MacNite/HiveInside/firmware-nrf54lm20a/src/mic.c

/* mic.c — see mic.h.
 *
 * The nRF54's PDM peripheral filters PDM to 16-bit PCM in hardware, so this
 * module only gathers PCM blocks through Zephyr's dmic API and runs the same
 * dBFS + FFT band analysis as HiveScale, so a band value means the same thing
 * across the ecosystem.
 *
 * The PDM clock only runs between DMIC_TRIGGER_START and _STOP, so the
 * microphone (powered from nPM1300 LDO1 — see power.c) draws its idle current
 * outside the ~0.7 s capture.
 *
 * The PDM controller is resolved by compatible, not by node label: any enabled
 * `nordic,nrf-pdm` node is used (the Sense board wires it to the on-board
 * MSM261DGT006). If the devicetree has none enabled, the module compiles to a
 * stub and the readout reports the mic absent.
 */
#include "mic.h"

#include "fft.h"
#include "hive_config.h"

#include <errno.h>
#include <math.h>
#include <zephyr/audio/dmic.h>
#include <zephyr/devicetree.h>
#include <zephyr/kernel.h>
#include <zephyr/sys/printk.h>

#if ENABLE_MIC && DT_HAS_COMPAT_STATUS_OKAY(nordic_nrf_pdm)

#define MIC_NODE DT_COMPAT_GET_ANY_STATUS_OKAY(nordic_nrf_pdm)

#define BLOCK_BYTES     (MIC_BLOCK_SAMPLES * sizeof(int16_t))
#define BLOCK_COUNT     6
#define READ_TIMEOUT_MS 1000

#define FULL_SCALE   32768.0f /* 16-bit PCM */
#define SILENCE_DBFS (-200.0f)

static const struct device *const dmic_dev = DEVICE_DT_GET(MIC_NODE);

K_MEM_SLAB_DEFINE_STATIC(mic_slab, BLOCK_BYTES, BLOCK_COUNT, 4);

/* FFT scratch + PCM staging, static like the accel path. */
static float fft_re[MIC_FFT_SAMPLE_COUNT];
static float fft_im[MIC_FFT_SAMPLE_COUNT];
static int16_t fft_pcm[MIC_FFT_SAMPLE_COUNT];

int mic_stream_start(void)
{
	if (!device_is_ready(dmic_dev)) {
		return -ENODEV;
	}
	struct pcm_stream_cfg stream = {
		.pcm_rate = MIC_SAMPLE_RATE, .pcm_width = 16,
		.block_size = BLOCK_BYTES, .mem_slab = &mic_slab,
	};
	struct dmic_cfg cfg = {
		.io = { .min_pdm_clk_freq = 1000000, .max_pdm_clk_freq = 3500000,
			.min_pdm_clk_dc = 40, .max_pdm_clk_dc = 60 },
		.streams = &stream,
		.channel = { .req_num_streams = 1, .req_num_chan = 1 },
	};
	cfg.channel.req_chan_map_lo = dmic_build_channel_map(0, 0, PDM_CHAN_LEFT);
	int err = dmic_configure(dmic_dev, &cfg);
	return err != 0 ? err : dmic_trigger(dmic_dev, DMIC_TRIGGER_START);
}

int mic_stream_read(void **buf, uint32_t *size, int32_t timeout_ms)
{
	return dmic_read(dmic_dev, 0, buf, size, timeout_ms);
}

void mic_stream_release(void *buf)
{
	k_mem_slab_free(&mic_slab, buf);
}

void mic_stream_stop(void)
{
	(void)dmic_trigger(dmic_dev, DMIC_TRIGGER_STOP);
}

static float band_energy_dbfs(const float *mag, float lo_hz, float hi_hz,
			      float norm)
{
	/* Parseval sum (no /count) so the value reflects real in-band acoustic
	 * energy and is comparable between bands of different widths — same
	 * convention as HiveScale. */
	float amp = hive_fft_band_amplitude(mag, MIC_FFT_SAMPLE_COUNT,
					    (float)MIC_SAMPLE_RATE, lo_hz,
					    hi_hz, norm, false);
	return amp > 0.0f ? 20.0f * log10f(amp) : SILENCE_DBFS;
}

static void compute_bands(size_t count, struct measurement *m)
{
	size_t n = MIN(count, (size_t)MIC_FFT_SAMPLE_COUNT);

	/* Centre the block on its mean so microphone DC bias does not leak
	 * through the Hann window side-lobes into the low bands. */
	float mean = 0.0f;

	for (size_t i = 0; i < n; i++) {
		mean += (float)fft_pcm[i];
	}
	if (n > 0) {
		mean /= (float)n;
	}
	for (size_t i = 0; i < n; i++) {
		fft_re[i] = ((float)fft_pcm[i] - mean) / FULL_SCALE;
		fft_im[i] = 0.0f;
	}
	for (size_t i = n; i < MIC_FFT_SAMPLE_COUNT; i++) {
		fft_re[i] = 0.0f;
		fft_im[i] = 0.0f;
	}

	hive_fft_hann(fft_re, MIC_FFT_SAMPLE_COUNT);
	hive_fft_magnitude(fft_re, fft_im, MIC_FFT_SAMPLE_COUNT);

	const float norm = ((float)MIC_FFT_SAMPLE_COUNT / 2.0f) * 0.5f;

	m->mic_band_sub_bass_dbfs = band_energy_dbfs(fft_re, MIC_BAND_SUBBASS_LO, MIC_BAND_SUBBASS_HI, norm);
	m->mic_band_hum_dbfs      = band_energy_dbfs(fft_re, MIC_BAND_HUM_LO, MIC_BAND_HUM_HI, norm);
	m->mic_band_piping_dbfs   = band_energy_dbfs(fft_re, MIC_BAND_PIPING_LO, MIC_BAND_PIPING_HI, norm);
	m->mic_band_stress_dbfs   = band_energy_dbfs(fft_re, MIC_BAND_STRESS_LO, MIC_BAND_STRESS_HI, norm);
	m->mic_band_high_dbfs     = band_energy_dbfs(fft_re, MIC_BAND_HIGH_LO, MIC_BAND_HIGH_HI, norm);
}

void mic_read(struct measurement *m)
{
	m->mic_ok = false;

	/* link's session gate is held for the complete measurement cycle, keeping
	 * this one-shot capture exclusive with audio's use of the PDM controller. */
	int err = mic_stream_start();
	if (err != 0) {
		printk("[MIC] start failed (%d)\n", err);
		return;
	}

	float sum = 0.0f, sum_sq = 0.0f;
	int16_t mn = INT16_MAX, mx = INT16_MIN;
	uint32_t count = 0;
	size_t fft_count = 0;
	unsigned block = 0;

	while (count < MIC_SAMPLE_FRAMES) {
		void *buf;
		uint32_t size;

		err = mic_stream_read(&buf, &size, READ_TIMEOUT_MS);
		if (err != 0) {
			printk("[MIC] read failed (%d) after %u frames\n", err,
			       (unsigned)count);
			break;
		}

		if (block++ < MIC_WARMUP_BLOCKS) {
			/* Discard: PDM filter + mic output still settling. */
			mic_stream_release(buf);
			continue;
		}

		const int16_t *pcm = buf;
		size_t frames = size / sizeof(int16_t);

		for (size_t i = 0; i < frames && count < MIC_SAMPLE_FRAMES; i++) {
			int16_t s = pcm[i];
			float f = (float)s;

			sum += f;
			sum_sq += f * f;
			if (s > mx) {
				mx = s;
			}
			if (s < mn) {
				mn = s;
			}
			if (fft_count < MIC_FFT_SAMPLE_COUNT) {
				fft_pcm[fft_count++] = s;
			}
			count++;
		}
		mic_stream_release(buf);
	}

	/* Stop the PDM clock between captures — the microphone consumes power
	 * whenever it is clocked. */
	mic_stream_stop();

	if (count == 0) {
		printk("[MIC] no PCM samples\n");
		return;
	}

	/* Remove DC offset; AC power = variance. */
	float mean = sum / (float)count;
	float variance = sum_sq / (float)count - mean * mean;

	if (variance < 0.0f) {
		variance = 0.0f;
	}
	float rms_norm = sqrtf(variance) / FULL_SCALE;

	m->mic_rms_dbfs = rms_norm > 0.0f ? 20.0f * log10f(rms_norm)
					  : SILENCE_DBFS;

	float dev_hi = (float)mx - mean;
	float dev_lo = mean - (float)mn;
	float peak_dev = dev_hi > dev_lo ? dev_hi : dev_lo;

	m->mic_peak_dbfs = peak_dev > 0.0f
				   ? 20.0f * log10f(peak_dev / FULL_SCALE)
				   : SILENCE_DBFS;
	m->mic_frames = count;
	if (fft_count < 64) {
		/* The MIC flag covers RMS, peak and all five bands. Setting it for a
		 * short capture left the uncomputed zero-initialized bands looking
		 * like valid full-scale audio, so reject the whole measurement. */
		printk("[MIC] only %u FFT samples; skipping\n",
		       (unsigned)fft_count);
		return;
	}

	compute_bands(fft_count, m);
	m->mic_ok = true;
}

#else /* !ENABLE_MIC or no nordic,nrf-pdm node enabled in the devicetree */

int mic_stream_start(void) { return -ENODEV; }
int mic_stream_read(void **buf, uint32_t *size, int32_t timeout_ms)
{
	ARG_UNUSED(buf); ARG_UNUSED(size); ARG_UNUSED(timeout_ms); return -ENODEV;
}
void mic_stream_release(void *buf) { ARG_UNUSED(buf); }
void mic_stream_stop(void) { }

void mic_read(struct measurement *m)
{
	m->mic_ok = false;
#if ENABLE_MIC
	printk("[MIC] no enabled nordic,nrf-pdm devicetree node — mic absent\n");
#endif
}

#endif
