MacNite/HiveInside/firmware-nrf54lm20a/src/mic.h

/* mic.h — on-board PDM microphone capture + acoustic FFT bands. */
#pragma once

#include "measurement.h"

#include <stdint.h>

int mic_stream_start(void);
int mic_stream_read(void **buf, uint32_t *size, int32_t timeout_ms);
void mic_stream_release(void *buf);
void mic_stream_stop(void);

/* The streaming and one-shot APIs share one PDM controller and must not
 * overlap.  link's session gate serialises an entire measurement cycle with
 * every BLE session before either path enters this module. */
/* Capture ~0.5 s of PCM from the PDM microphone and reduce it to RMS/peak dBFS
 * plus the five shared acoustic bands (sets m->mic_ok). A no-op that leaves
 * mic_ok false when the devicetree has no enabled nRF PDM node. */
void mic_read(struct measurement *m);
