MacNite/HiveInside/firmware-nrf54lm20a/src/beacon.h

/* HiveHub-compatible, connectionless BLE measurement transport. */
#pragma once

#include "measurement.h"

/* Enable Bluetooth. Advertising starts with the first published reading. */
int beacon_init(void);

/* Encode and publish one measurement. The controller repeats it autonomously. */
int beacon_publish(const struct measurement *measurement);

/* Maintain the legacy advertising set around a peripheral connection. */
void beacon_connected(void);
void beacon_disconnected(void);
