MacNite/HiveInside/firmware-nrf54lm20a/src/audio_secret.example.h

/* Copy to audio_secret.h and replace every byte with a securely generated key.
 * The real file is gitignored; an all-zero key deliberately disables START. */
#pragma once
#include <stdint.h>
static const uint8_t hive_audio_psk[32] = {
	0x00, 0x00, 0x00, 0x00, 0x00, 0x00, 0x00, 0x00,
	0x00, 0x00, 0x00, 0x00, 0x00, 0x00, 0x00, 0x00,
	0x00, 0x00, 0x00, 0x00, 0x00, 0x00, 0x00, 0x00,
	0x00, 0x00, 0x00, 0x00, 0x00, 0x00, 0x00, 0x00,
};
